DeuceEFI/USBDM/USBDM.sch

## KiCad design USBDM.sch (2012-04-23)

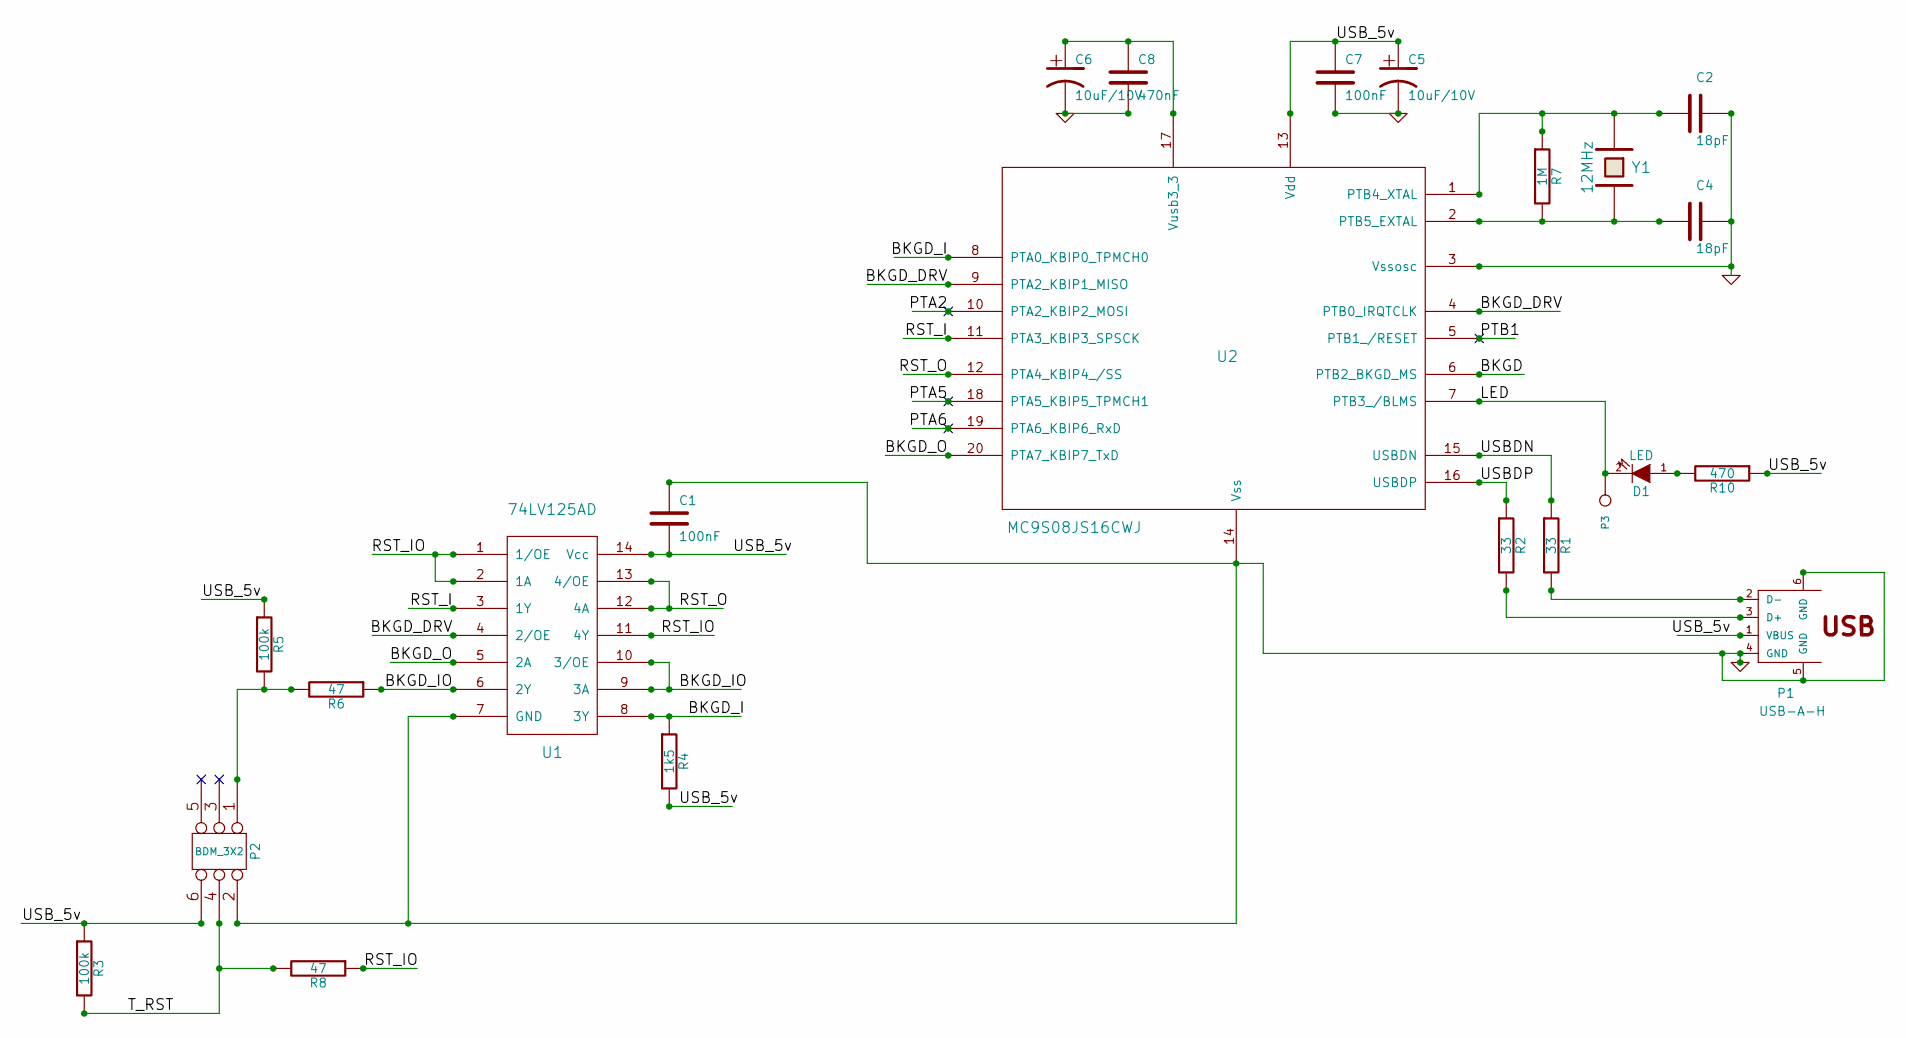
[picture p6: schematic USBDM.sch]

Parts:
C1, C7: 100nF
C2, C4: 18pF
C5, C6: 10uF/10V
C8: 470nF
D1: LED
P1: USB-A-H; con-usb-3-USB-A-H
P2: BDM_3X2
P3: BL
R1, R2: 33
R3, R5: 100k
R4: 1k5
R6, R8: 47
R7: 1M
R10: 470
U1: 74LV125AD
U2: MC9S08JS16CWJ
Y1: 12MHz

Connections:
BKGD: U2.6 (PTB2_BKGD_MS)
BKGD_DRV: U1.4 (2/OE), U2.4 (PTB0_IRQTCLK), U2.9 (PTA2_KBIP1_MISO)
BKGD_I: R4.1, U1.8 (3Y), U2.8 (PTA0_KBIP0_TPMCH0)
BKGD_IO: R6.1, U1.6 (2Y), U1.9 (3A), U1.10 (3/OE)
BKGD_O: U1.5 (2A), U2.20 (PTA7_KBIP7_TxD)
GND: C1.1, C2.1, C4.1, C5.2 (-), C6.2 (-), C7.2, C8.2, P1.4 (GND), P1.5 (GND), P1.6 (GND), P2.2, U1.7 (GND), U2.3 (Vssosc), U2.14 (Vss)
LED: D1.2 (K), P3.1, U2.7 (PTB3_/BLMS)
unnamed: C2.2, R7.1, U2.1 (PTB4_XTAL), Y1.1
unnamed: C4.2, R7.2, U2.2 (PTB5_EXTAL), Y1.2
unnamed: C6.1 (+), C8.1, U2.17 (Vusb3_3)
unnamed: D1.1 (A), R10.2
unnamed: P1.2 (D-), R1.2
unnamed: P1.3 (D+), R2.2
unnamed: P2.1, R5.2, R6.2
PTA2: U2.10 (PTA2_KBIP2_MOSI)
PTA5: U2.18 (PTA5_KBIP5_TPMCH1)
PTA6: U2.19 (PTA6_KBIP6_RxD)
PTB1: U2.5 (PTB1_/RESET)
RST_I: U1.3 (1Y), U2.11 (PTA3_KBIP3_SPSCK)
RST_IO: R8.1, U1.1 (1/OE), U1.2 (1A), U1.11 (4Y)
RST_O: U1.12 (4A), U1.13 (4/OE), U2.12 (PTA4_KBIP4_/SS)
T_RST: P2.4, R3.2, R8.2
USBDN: R1.1, U2.15 (USBDN)
USBDP: R2.1, U2.16 (USBDP)
USB_5v: C1.2, C5.1 (+), C7.1, P1.1 (VBUS), P2.6, R3.1, R4.2, R5.1, R10.1, U1.14 (Vcc), U2.13 (Vdd)
